S-March/dEEbugger_Public/Pictures/05.png

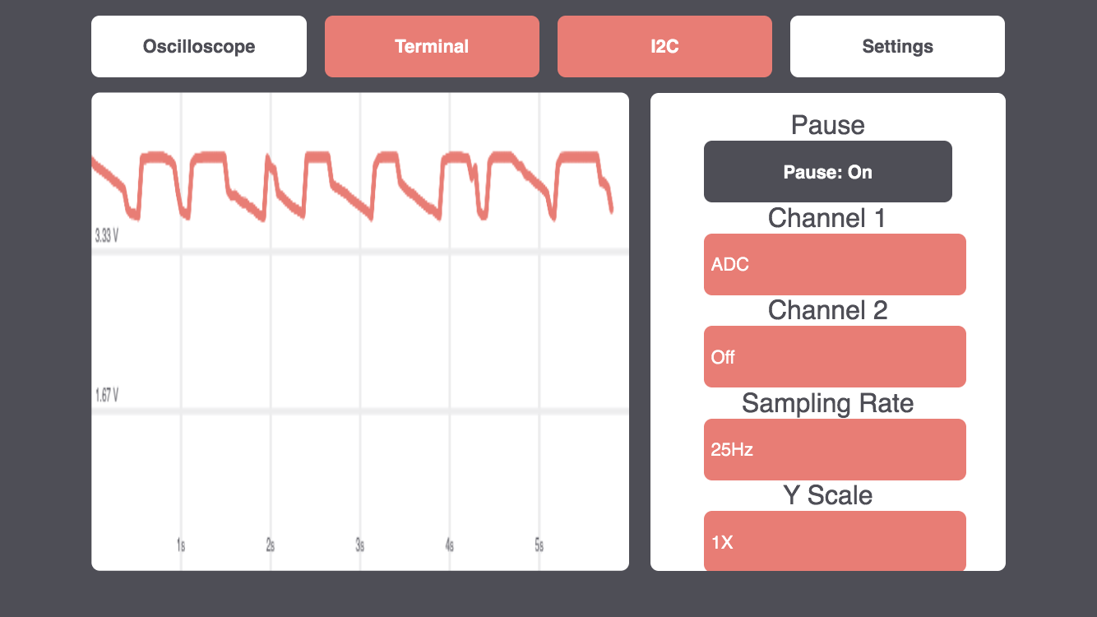
Pictures/05.png
