S-March/dEEbugger_Public/Pictures/08.png

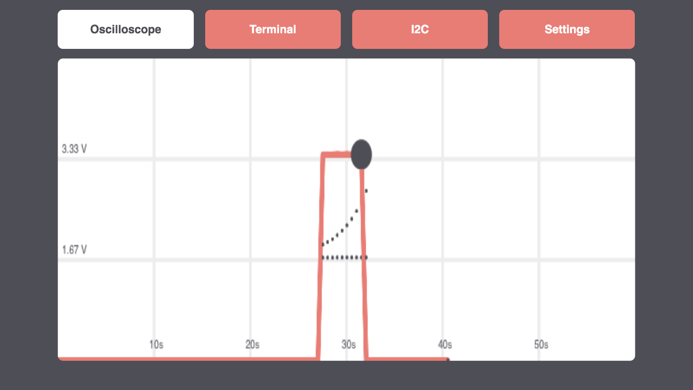
Pictures/08.png
