S-March/dEEbugger_Public/Pictures/12.png

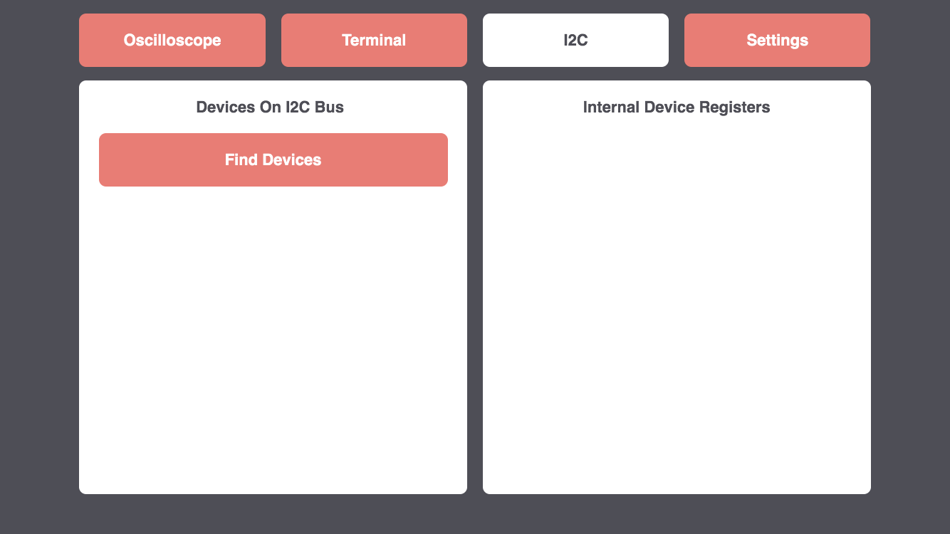
Pictures/12.png
