S-March/dEEbugger_Public/Software/dEEbugger/WebsocketInterpreter.cpp

#include "WebsocketInterpreter.h"

void webSocketDataInterpreter(WebSocketsServer &WEBSOCKETOBJECT, String WEBSOCKETDATA)
{
  String topLevelToken = "";
  String subLevelToken = "";
  String serialClear = "SERIAL UART CLEAR";
  Serial.println("New data received: " + WEBSOCKETDATA);
  
  //I2C related tasks
  if(WEBSOCKETDATA.startsWith("I2C"))
  {
    //Look at start of line for tokens, add +1 to length to account for space
    topLevelToken = "I2C";
    String i2cCommand = WEBSOCKETDATA.substring(topLevelToken.length()+1);
    if(i2cCommand.startsWith("SCAN"))
    {
      WEBSOCKETOBJECT.broadcastTXT(serialClear);
      scanI2CAddressAndRegisters(WEBSOCKETOBJECT);
    }
    if(i2cCommand.startsWith("FIND DEVICES"))
    {
      WEBSOCKETOBJECT.broadcastTXT(serialClear);
      scanI2CAddress(WEBSOCKETOBJECT);
    }    
    if(i2cCommand.startsWith("READ DEVICE"))
    {
      WEBSOCKETOBJECT.broadcastTXT(serialClear);
      //Look at start of line for subtokens, add +1 to length to account for space
      subLevelToken = "READ DEVICE";
      byte deviceToRead = i2cCommand.substring(subLevelToken.length()+1).toInt();
      scanI2CRegisters(WEBSOCKETOBJECT, deviceToRead);
    }
  }
  //Oscilloscope related tasks
  if(WEBSOCKETDATA.startsWith("SCOPE"))
  {
    //Look at start of line for tokens, add +1 to length to account for space
    topLevelToken = "SCOPE";
    String scopeCommand = WEBSOCKETDATA.substring(topLevelToken.length()+1);
    if(scopeCommand.startsWith("CHANNEL 1"))
    {
      //Look at start of line for subtokens, add +1 to length to account for space
      subLevelToken = "CHANNEL 1";
      setChannelMode1(scopeCommand.substring(subLevelToken.length()+1));
    }
    if(scopeCommand.startsWith("CHANNEL 2"))
    {
      //Look at start of line for subtokens, add +1 to length to account for space
      subLevelToken = "CHANNEL 2";
      setChannelMode2(scopeCommand.substring(subLevelToken.length()+1));
    }
    if(scopeCommand.startsWith("TIMESCALE"))
    {
      //Look at start of line for subtokens, add +1 to length to account for space
      subLevelToken = "TIMESCALE";
      setMsTimer(scopeCommand.substring(subLevelToken.length()+1).toInt());
    }
    if(scopeCommand.startsWith("DATALOG"))
    {
      //Look at start of line for subtokens, add +1 to length to account for space
      subLevelToken = "DATALOG";
      if(scopeCommand.substring(subLevelToken.length()+1) == "ON")
      {
        setDataLog(true);
      }
      else
      {
        setDataLog(false);
      }
    }
  }
  //Terminal related tasks
  if(WEBSOCKETDATA.startsWith("TERMINAL"))
  {
    //Look at start of line for tokens, add +1 to length to account for space
    topLevelToken = "TERMINAL";
    String terminalCommand = WEBSOCKETDATA.substring(topLevelToken.length()+1);
    if(terminalCommand.startsWith("CONNECT"))
    {
      //Look at start of line for subtokens, add +1 to length to account for space
      subLevelToken = "CONNECT";
      if(terminalCommand.substring(subLevelToken.length()+1) == "ON")
      {
        //CONNECT TO SERIAL
      }
      else
      {
        //DISCONNECT FROM SERIAL
      }
    }
  }
}
